bkw777/WP-2_IC-Card/COVER/out_/WP-2_IC-Card_Cover_SRAM.png

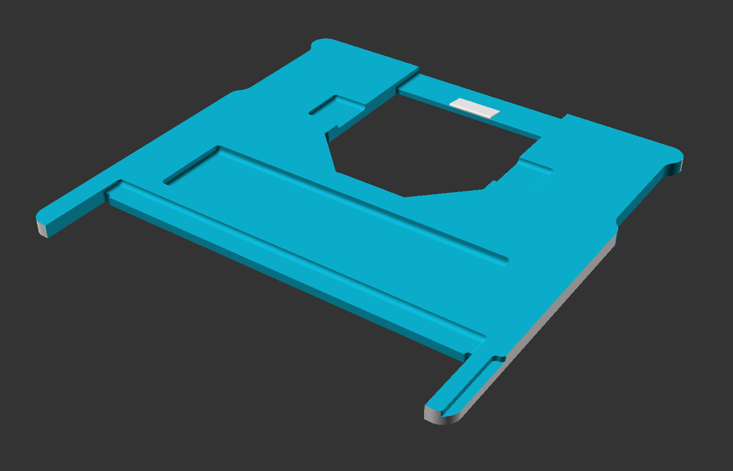
COVER/out_/WP-2_IC-Card_Cover_SRAM.png
