bkw777/WP-2_IC-Card/PCB/out/WP-2_IC-Card_Breakout.top.jpg

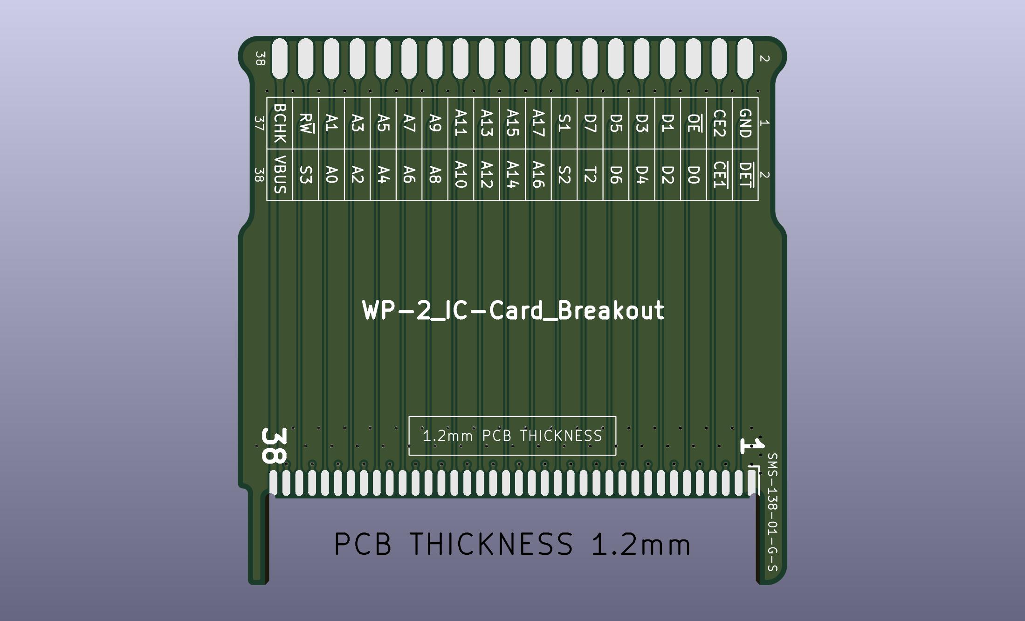
PCB/out/WP-2_IC-Card_Breakout.top.jpg
