bkw777/WP-2_IC-Card/PCB/out/WP-2_IC-Card_BUS_TAP.bottom.jpg

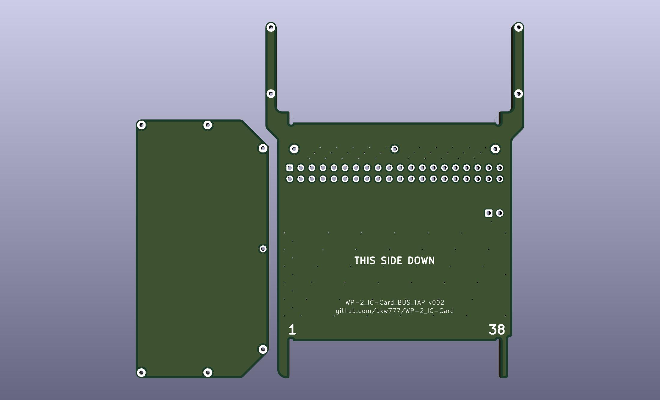
PCB/out/WP-2_IC-Card_BUS_TAP.bottom.jpg
