bkw777/WP-2_IC-Card/PCB/out/WP-2_IC-Card_BUS_TAP.top.jpg

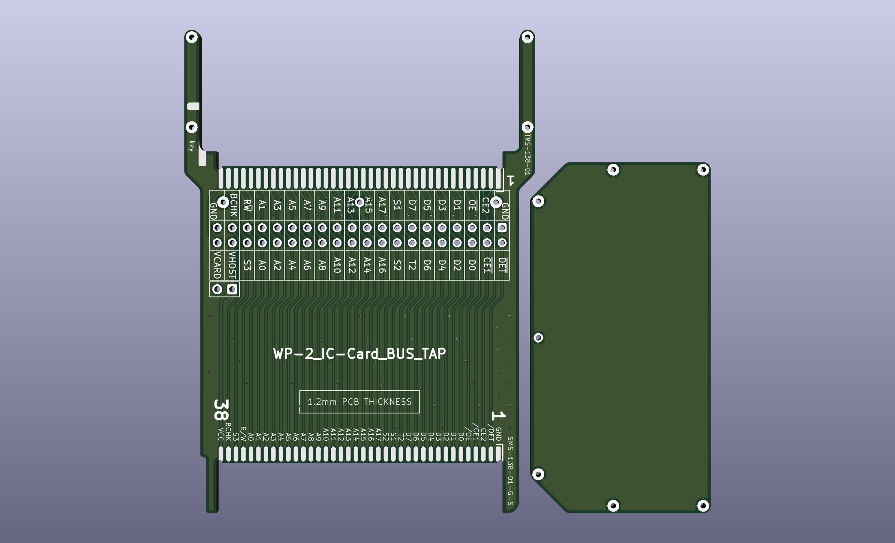
PCB/out/WP-2_IC-Card_BUS_TAP.top.jpg
