bkw777/WP-2_IC-Card/PCB/out/WP-2_IC-Card_MRAM.no_bank_pcb.jpg

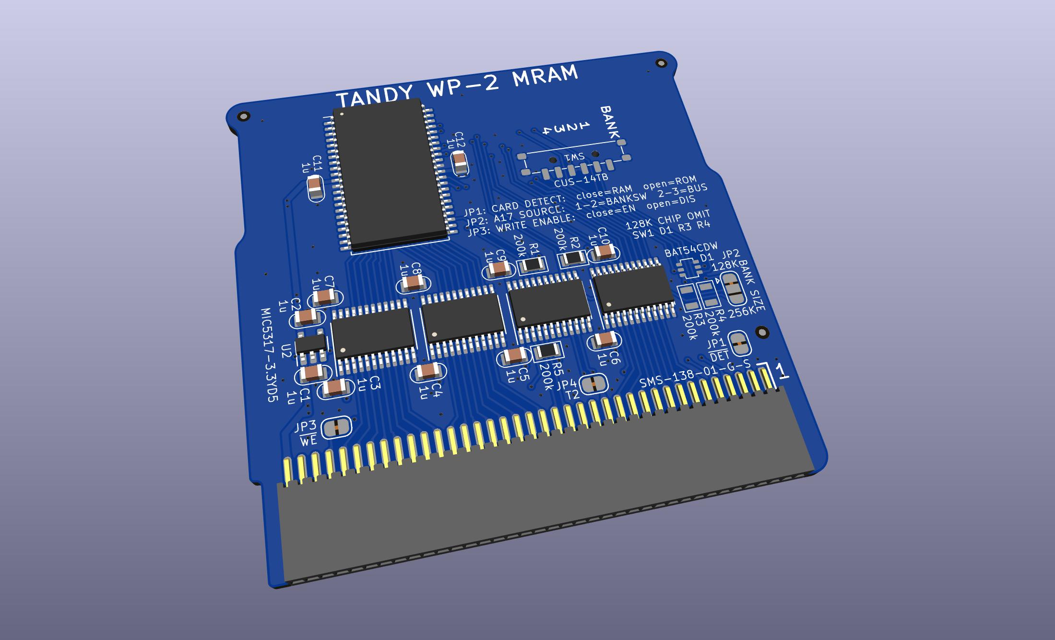
PCB/out/WP-2_IC-Card_MRAM.no_bank_pcb.jpg
