bkw777/WP-2_IC-Card/PCB/out/WP-2_IC-Card_MRAM_2.jpg

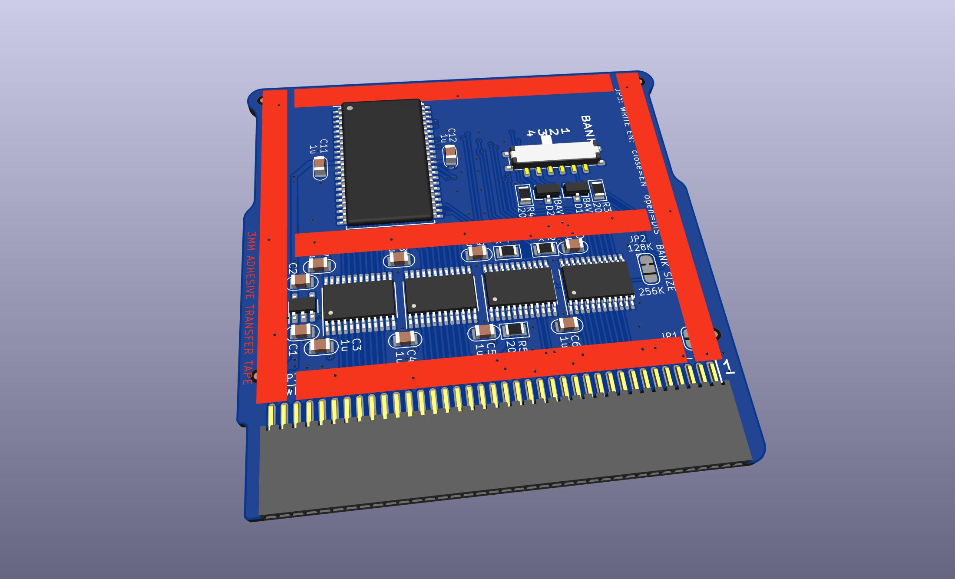
PCB/out/WP-2_IC-Card_MRAM_2.jpg
