bkw777/WP-2_IC-Card/PCB/out/WP-2_IC-Card_MRAM_3.jpg

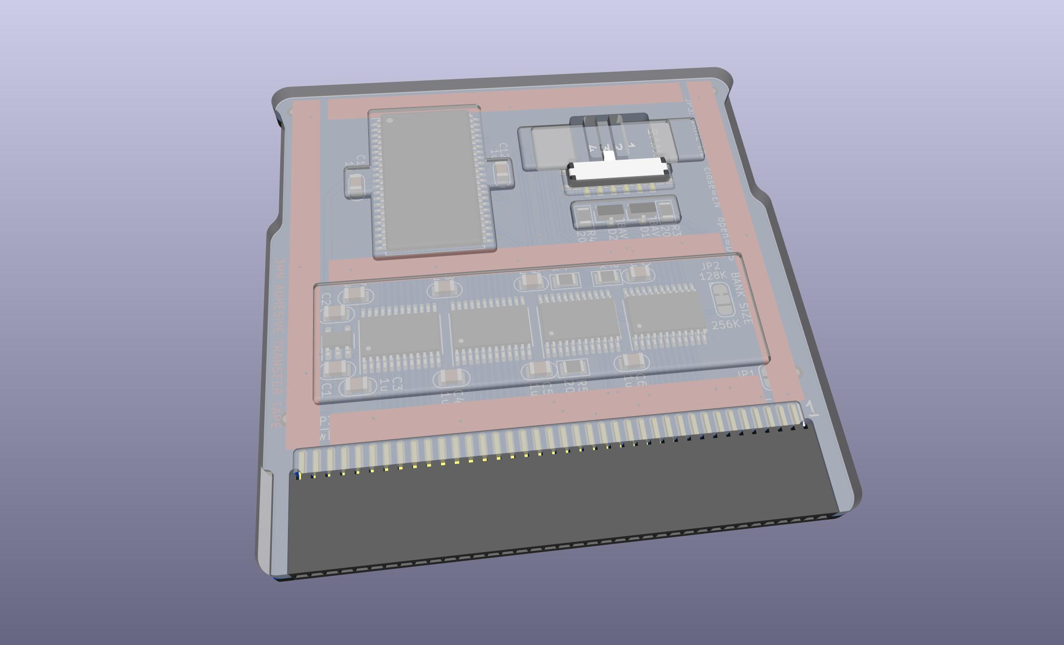
PCB/out/WP-2_IC-Card_MRAM_3.jpg
