bkw777/WP-2_IC-Card/PCB/out/WP-2_IC-Card_MRAM_128K.jpg

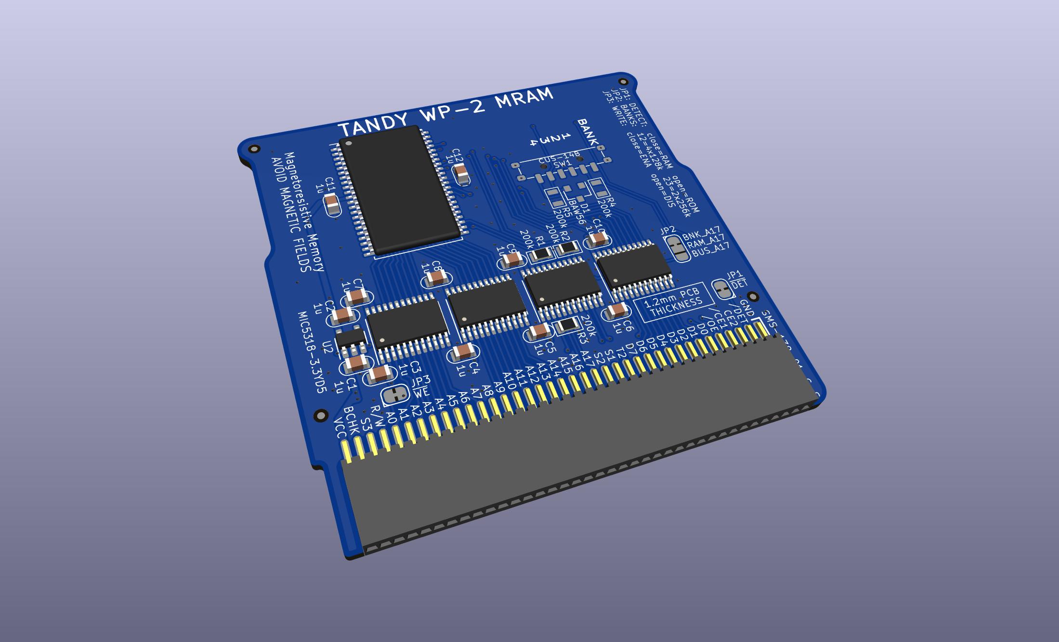
PCB/out/WP-2_IC-Card_MRAM_128K.jpg
