bkw777/WP-2_IC-Card/PCB/out/WP-2_IC-Card_Programming_Adapter.bottom.jpg

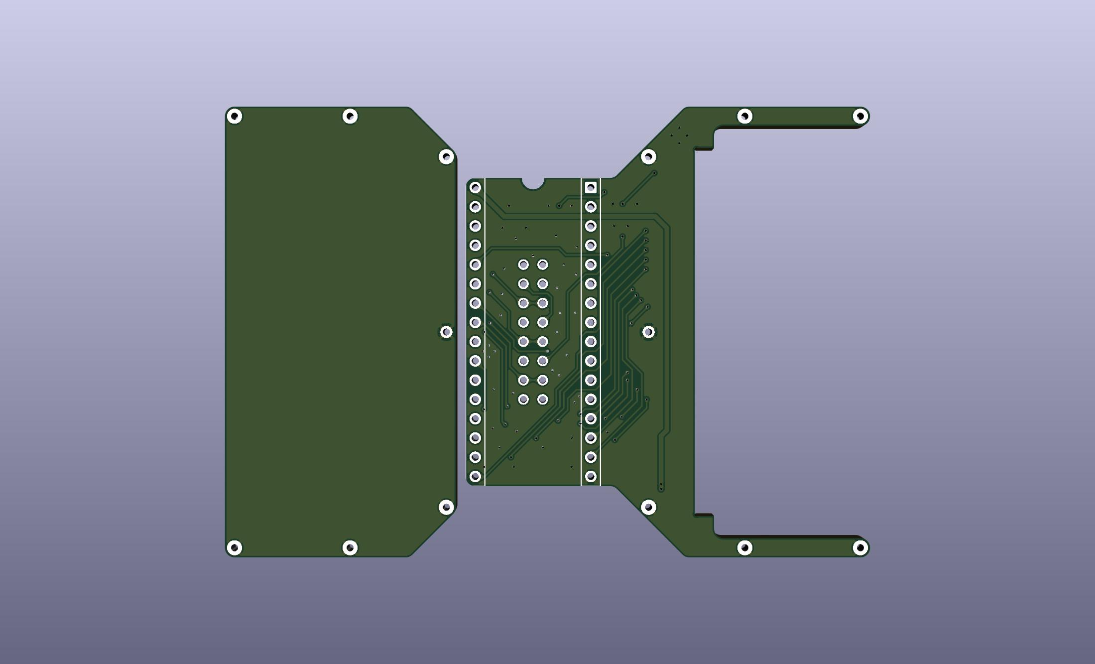
PCB/out/WP-2_IC-Card_Programming_Adapter.bottom.jpg
