bkw777/WP-2_IC-Card/PCB/out/WP-2_IC-Card_Programming_Adapter.top.jpg

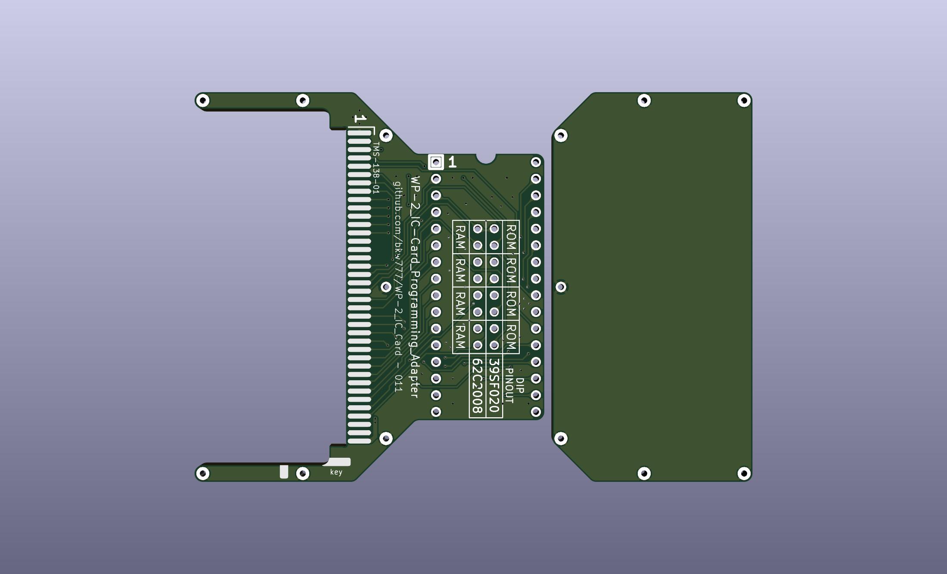
PCB/out/WP-2_IC-Card_Programming_Adapter.top.jpg
