bkw777/WP-2_IC-Card/ref/3D7_LVC4245A.png

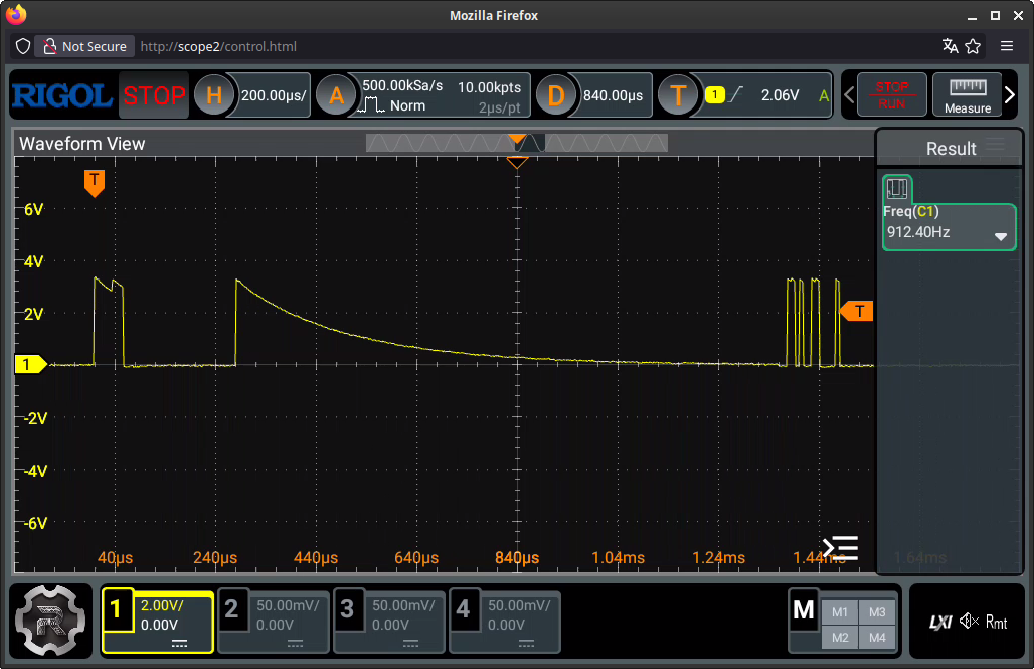
ref/3D7_LVC4245A.png
