bkw777/WP-2_IC-Card/ref/20250928_230935498.JPG

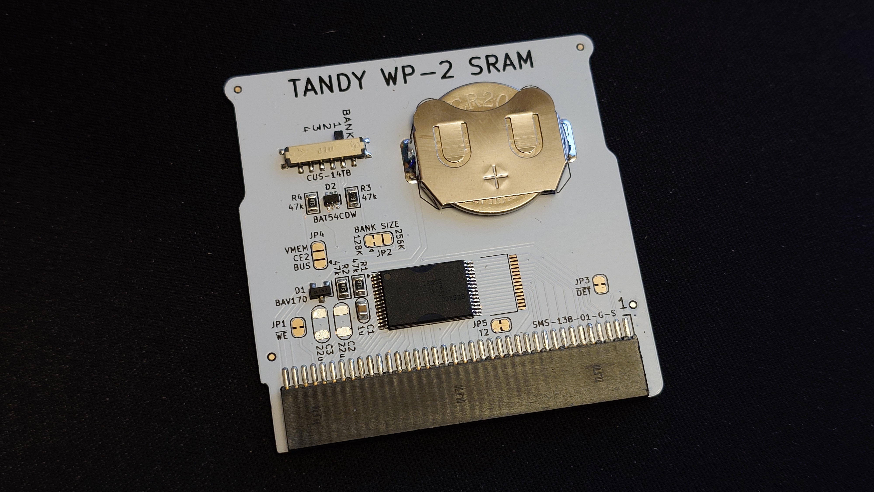
ref/20250928_230935498.JPG
