bkw777/WP-2_IC-Card/ref/bent_pin.jpg

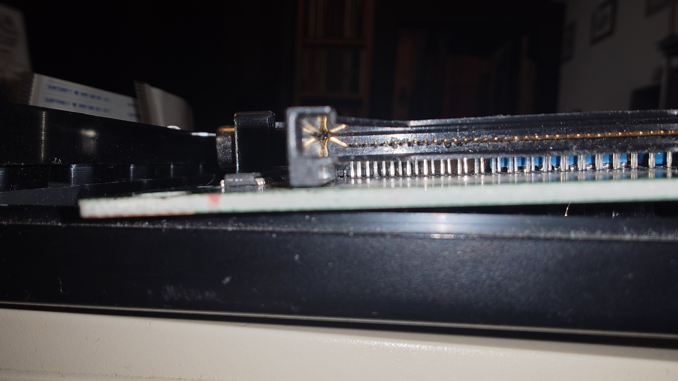
ref/bent_pin.jpg
