bkw777/WP-2_IC-Card/ref/bus_tap.2.jpg

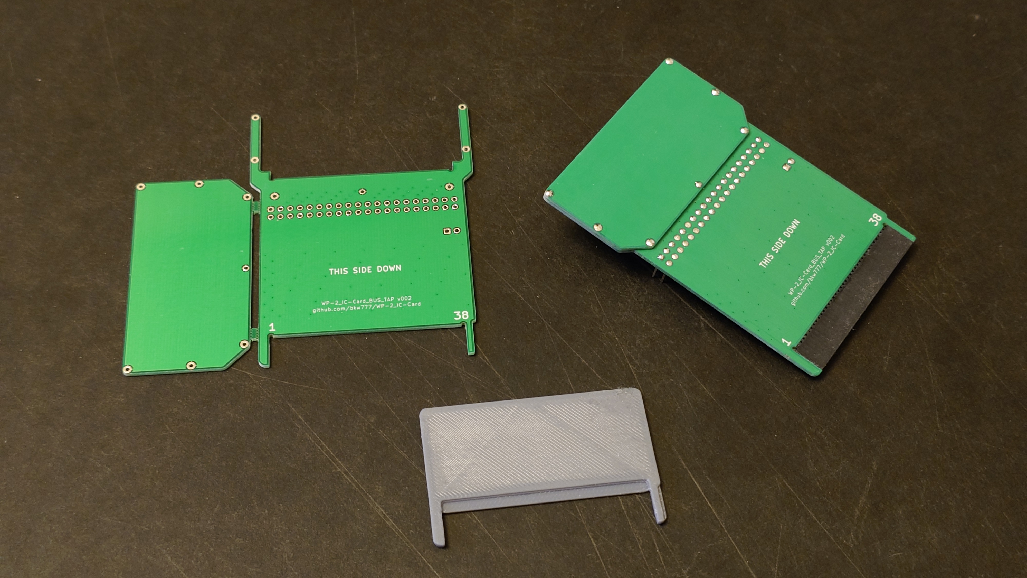
ref/bus_tap.2.jpg
