bkw777/WP-2_IC-Card/ref/CBM-10WP.jpg

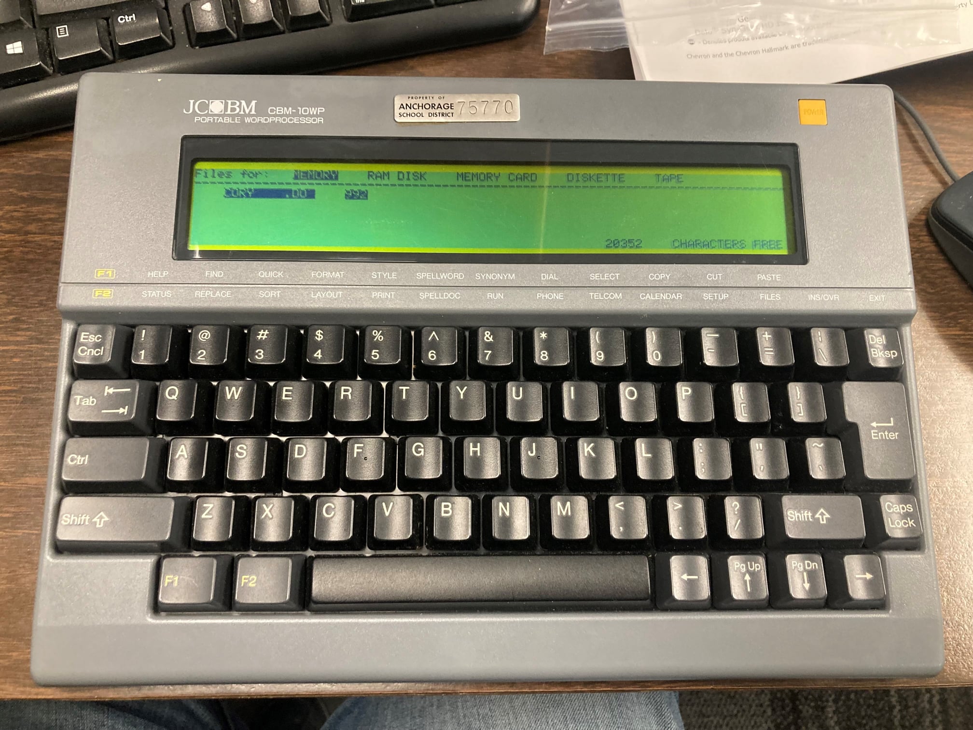
ref/CBM-10WP.jpg
