bkw777/WP-2_IC-Card/ref/TSOP32-programming-adapter.jpg

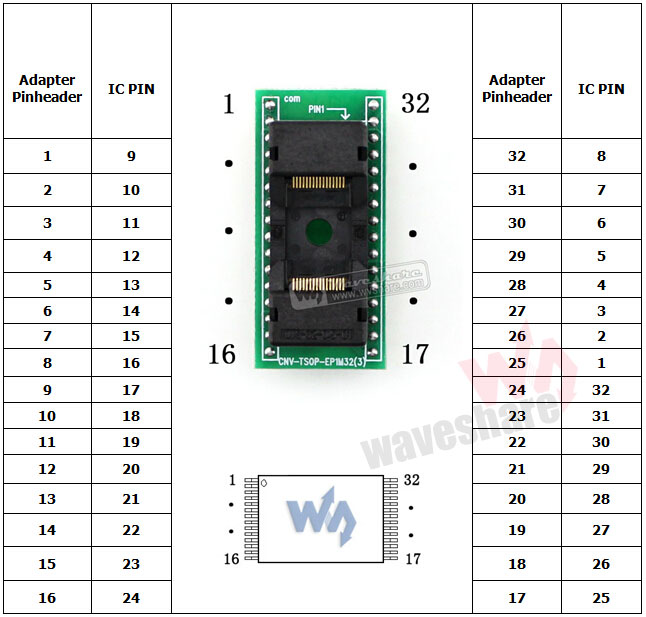
ref/TSOP32-programming-adapter.jpg
